arm-n/ESP-WROOM-32-Development-Board/images/Screenshot 2026-09-27 at 7.58.38 PM.png

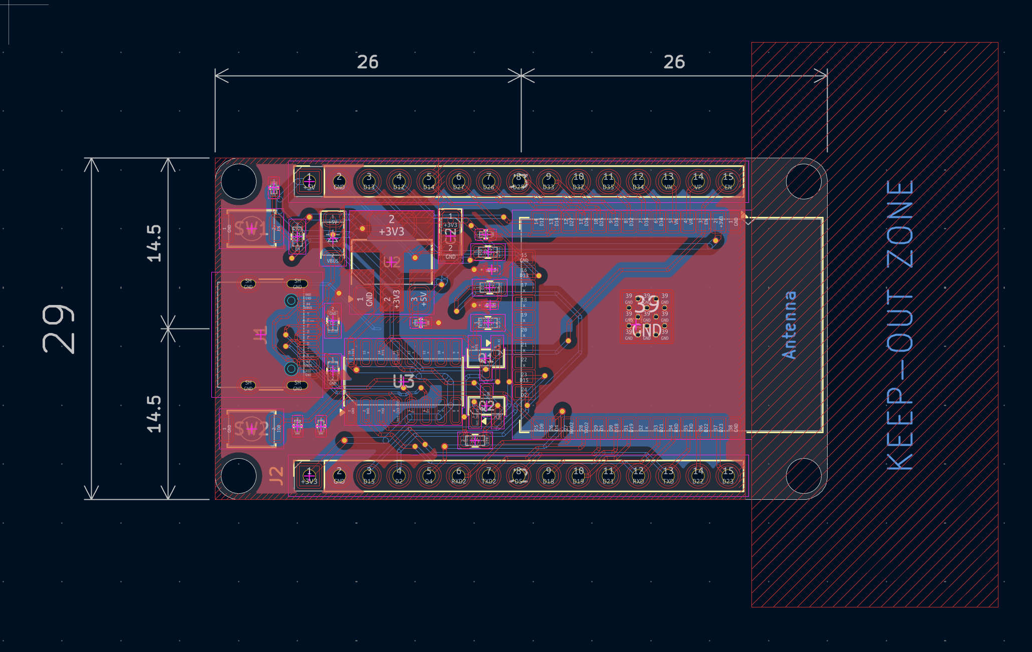
images/Screenshot 2026-09-27 at 7.58.38 PM.png
