arm-n/ESP-WROOM-32-Development-Board/images/Screenshot 2026-09-27 at 7.59.09 PM.png

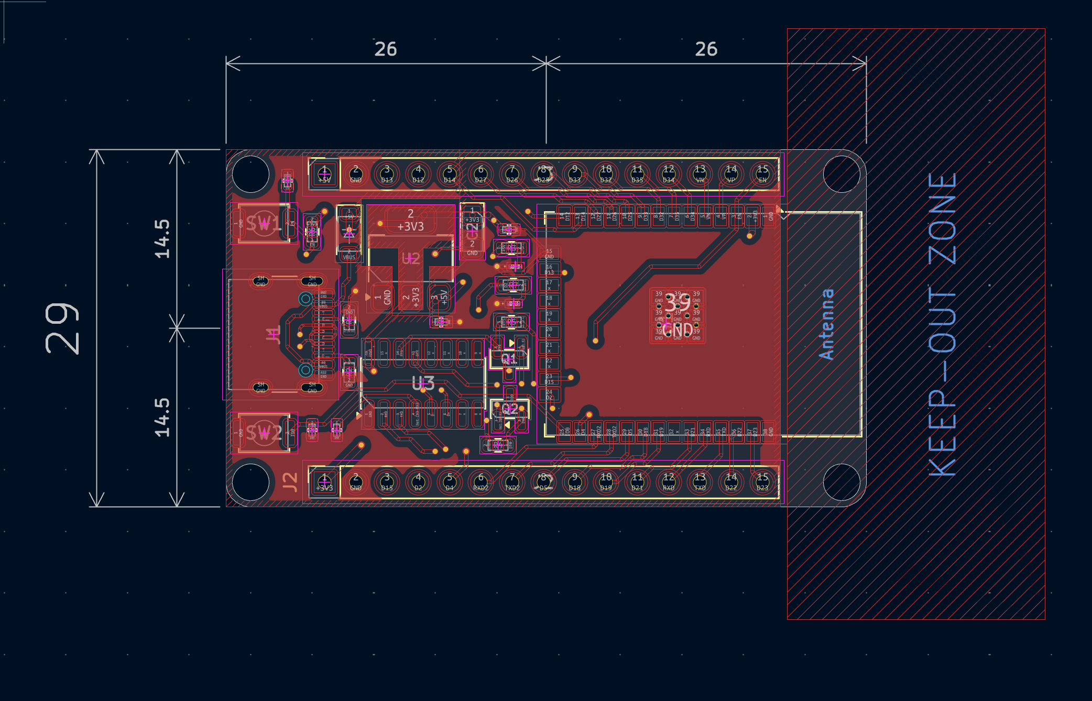
images/Screenshot 2026-09-27 at 7.59.09 PM.png
