arm-n/ESP-WROOM-32-Development-Board/images/Screenshot 2026-09-27 at 8.05.48 PM.png

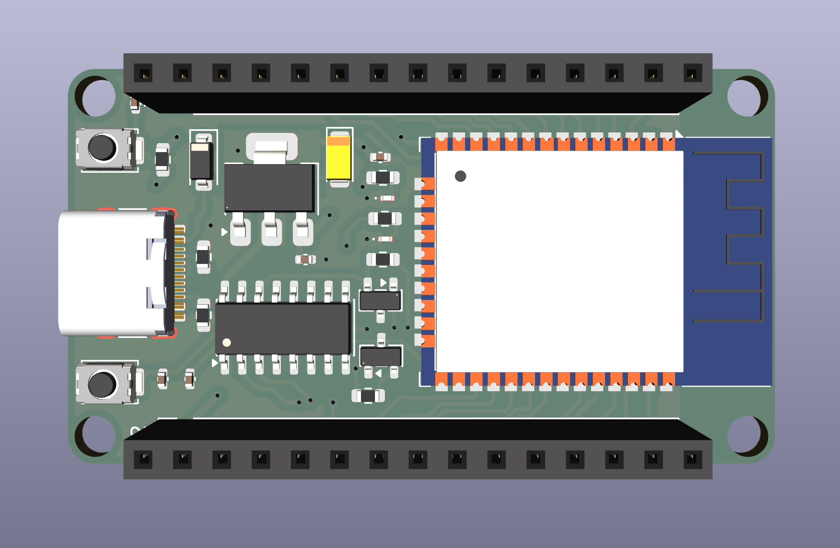
images/Screenshot 2026-09-27 at 8.05.48 PM.png
